dorsic/pragoPi/images/IMG_1538.jpg

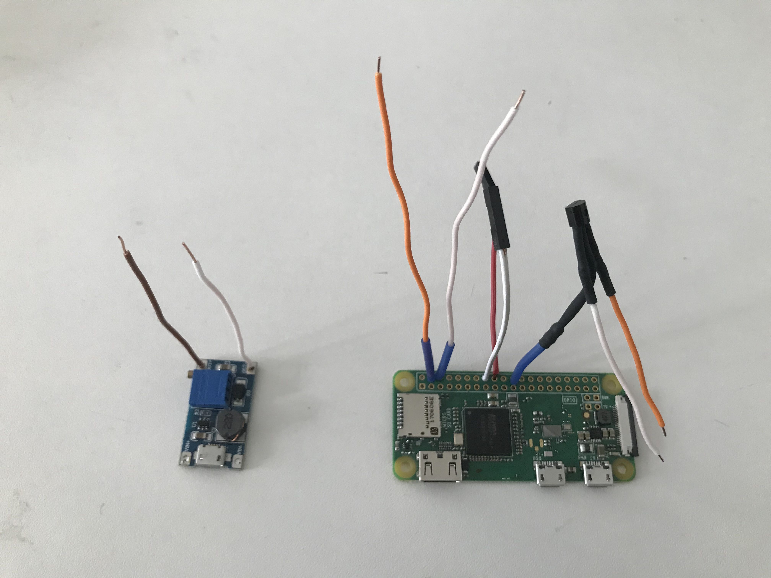
images/IMG_1538.jpg
