dorsic/pragoPi/images/IMG_1539.jpg

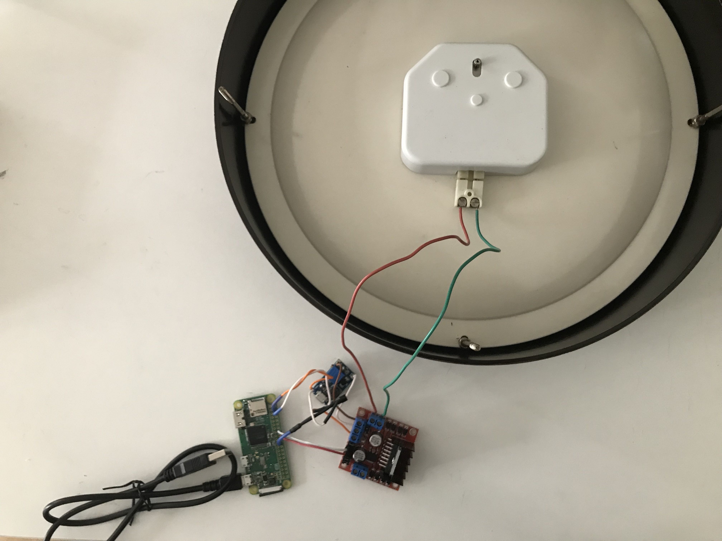
images/IMG_1539.jpg
