dorsic/pragoPi/images/IMG_1540.jpg

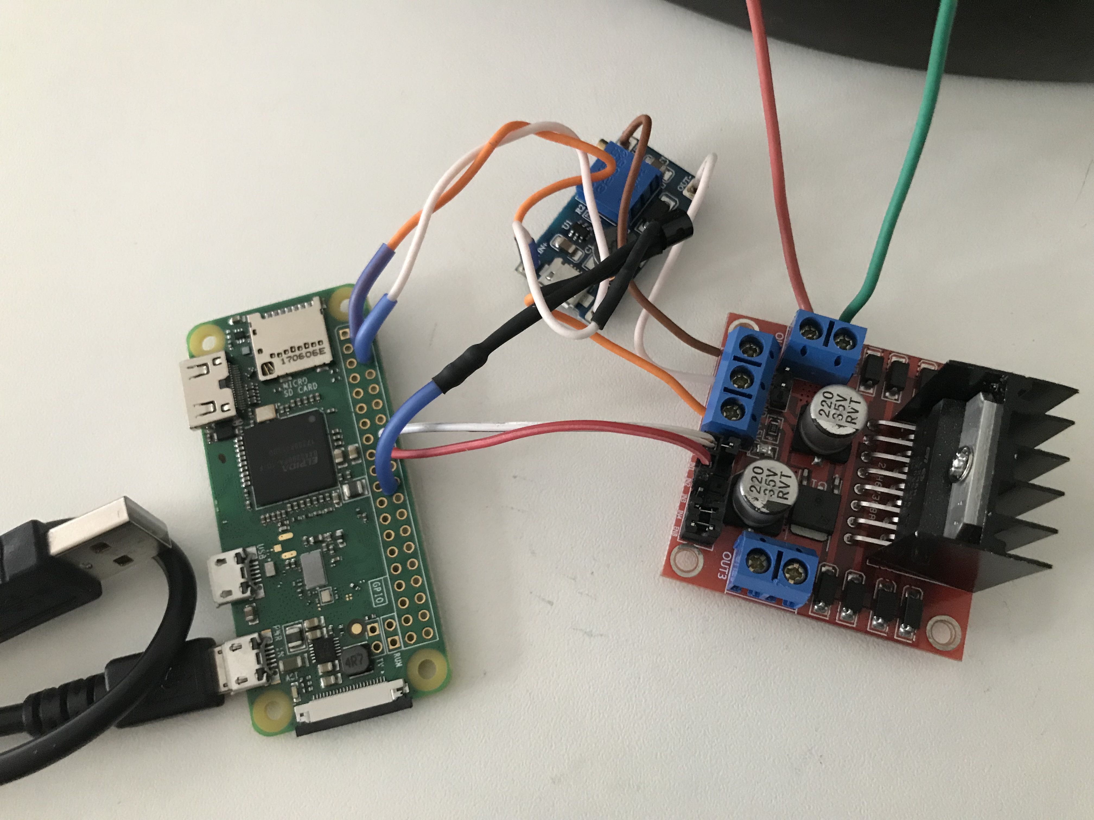
images/IMG_1540.jpg
