dorsic/pragoPi/images/IMG_1543.jpg

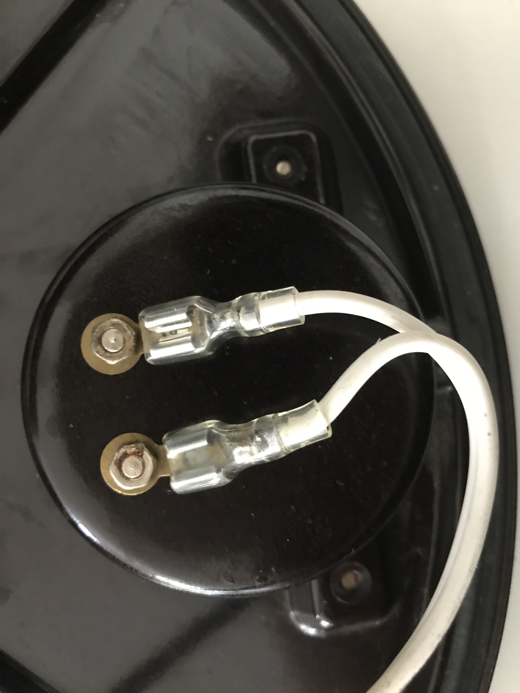
images/IMG_1543.jpg
