dorsic/pragoPi/images/IMG_1544.jpg

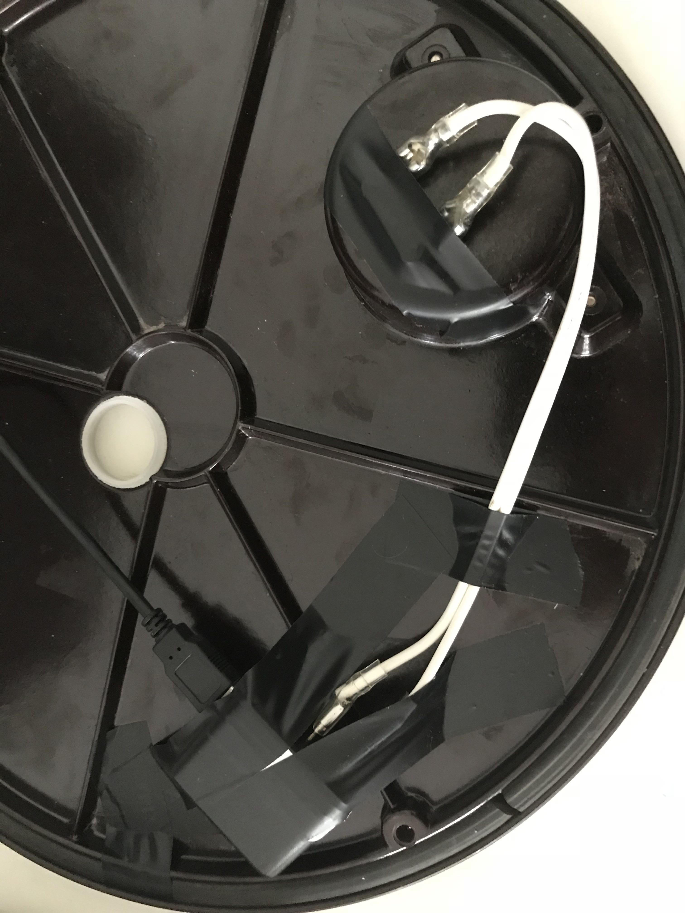
images/IMG_1544.jpg
