dorsic/pragoPi/images/IMG_1549.jpg

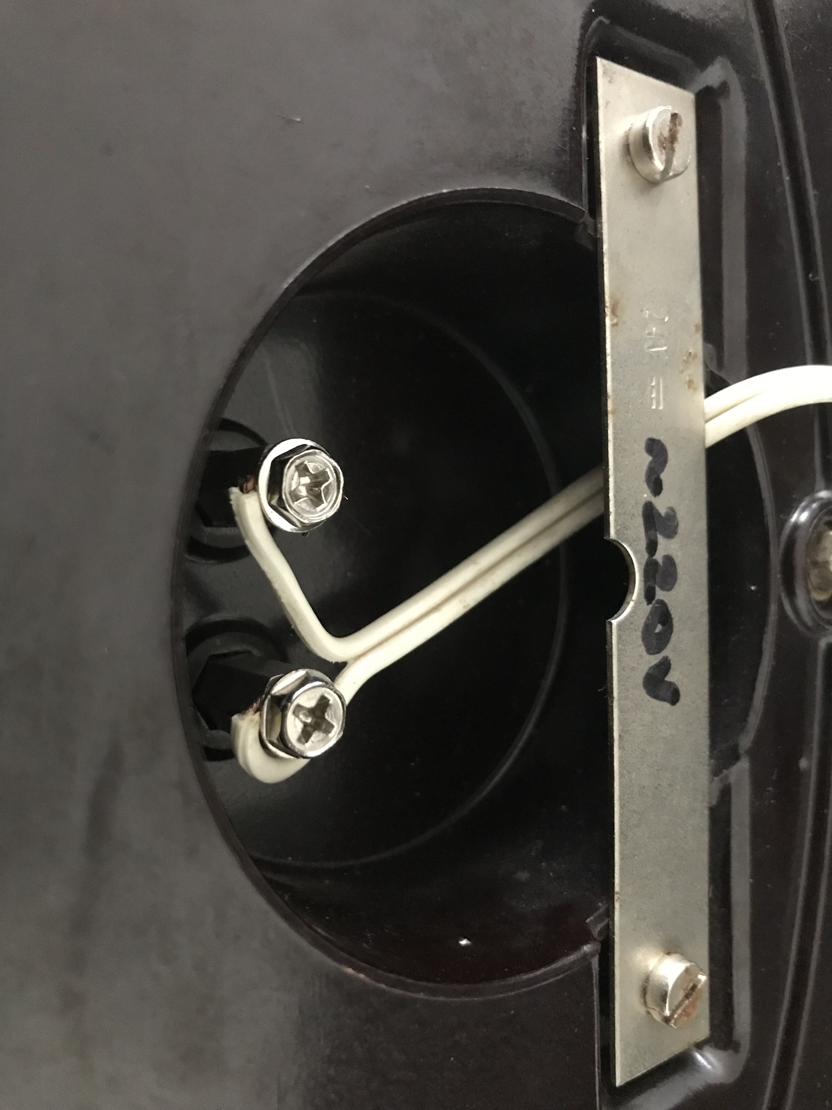
images/IMG_1549.jpg
